isandrocks/Skyline_20K/20Key_macropad.kicad_sch

## KiCad design 20Key_macropad.kicad_sch (2024-02-22)

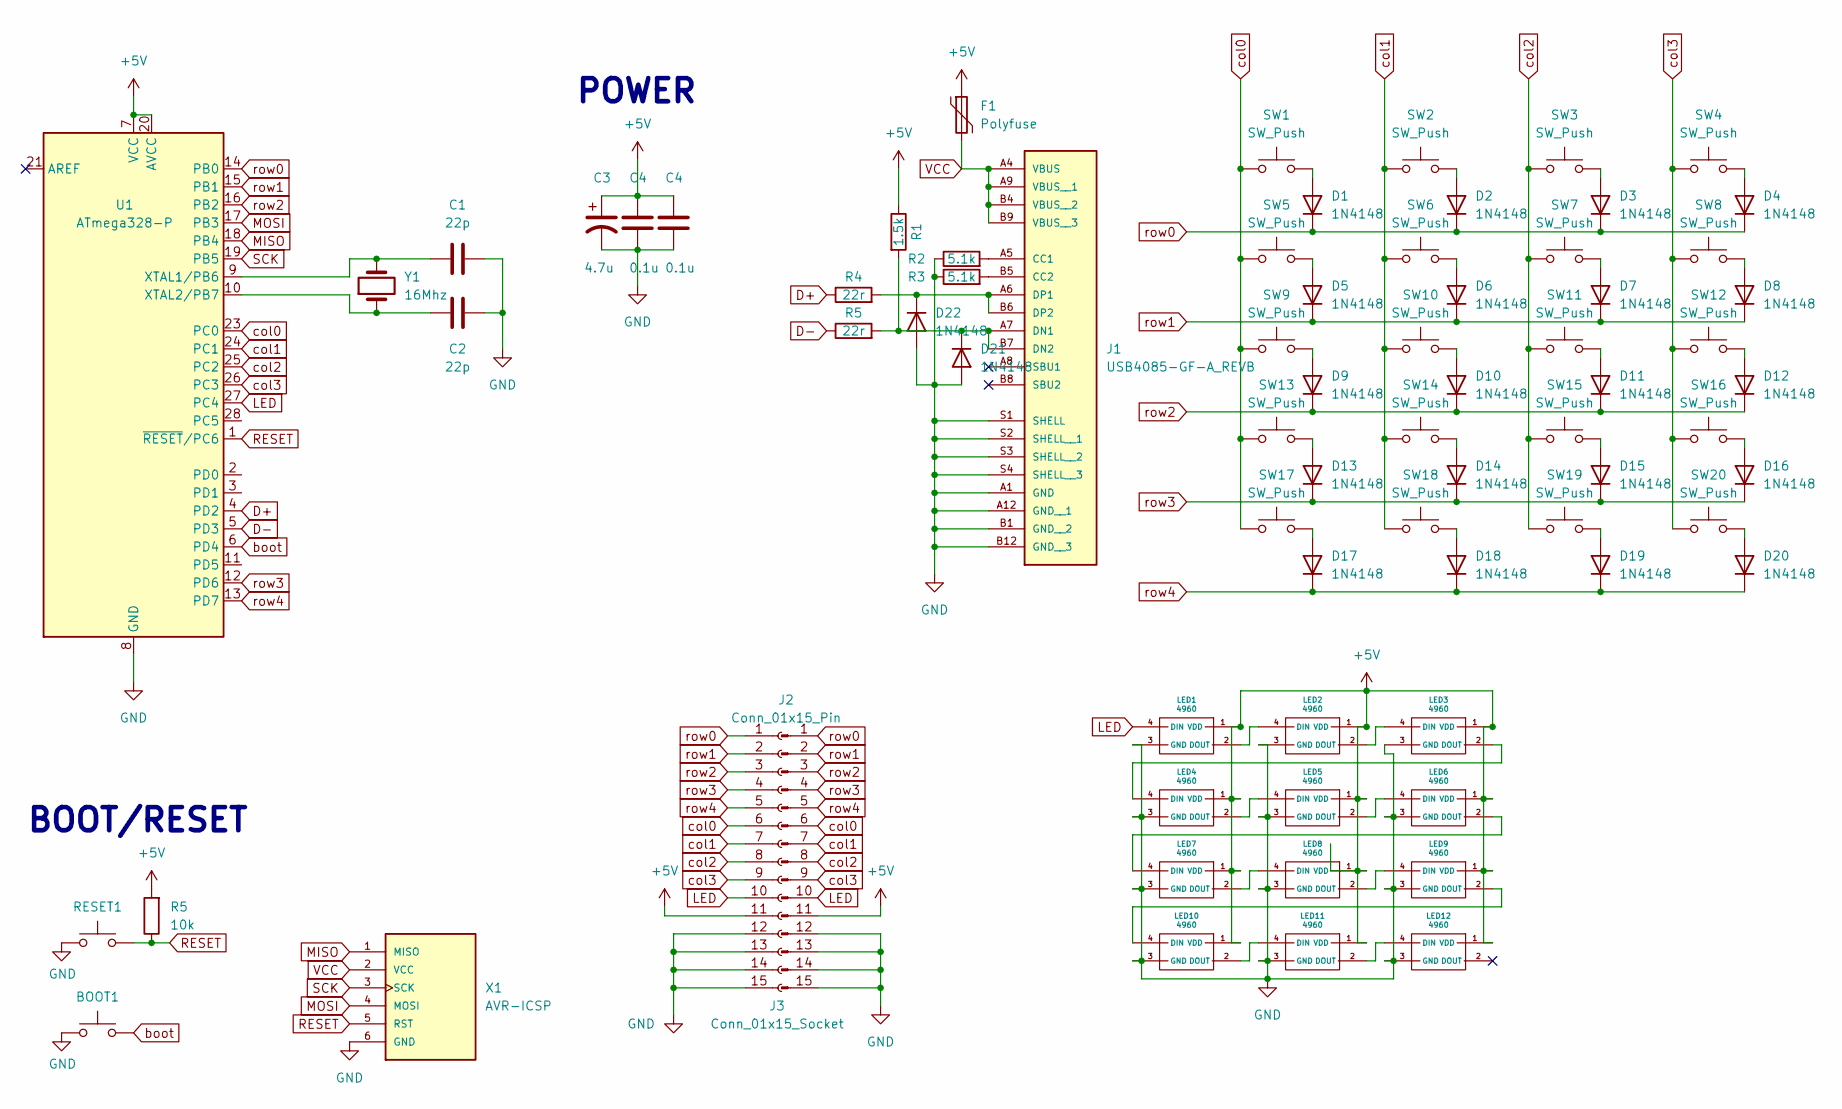
[picture p2: schematic 20Key_macropad.kicad_sch]

Parts:
BOOT1: SW_Push; SW_PUSH_6mm
C1, C2: 22p; C_Disc_D4.3mm_W1.9mm_P5.00mm
C3: 4.7u; CP_Radial_D5.0mm_P2.50mm
C4: 0.1u; C_Disc_D3.0mm_W2.0mm_P2.50mm
D1, D2, D3, D4, D5, D6, D7, D8, D9, D10, D11, D12, D13, D14, D15, D16, D17, D18, D19, D20: 1N4148; D_SOD-123
D21, D22: 1N4148; D_DO-35_SOD27_P7.62mm_Horizontal
F1: Polyfuse; C_Disc_D7.5mm_W2.5mm_P5.00mm
J1: USB4085-GF-A_REVB; GCT_USB4085-GF-A_REVB; PARTREV B
J2: Conn_01x15_Pin; PinHeader_1x15_P2.54mm_Vertical
J3: Conn_01x15_Socket; PinHeader_1x15_P2.54mm_Vertical
LED1, LED2, LED3, LED4, LED5, LED6, LED7, LED8, LED9, LED10, LED11, LED12: 4960; 4960_ADA
R1: 1.5k; R_Axial_DIN0204_L3.6mm_D1.6mm_P5.08mm_Horizontal
R2, R3: 5.1k; R_Axial_DIN0204_L3.6mm_D1.6mm_P5.08mm_Horizontal
R4: 22r; R_Axial_DIN0204_L3.6mm_D1.6mm_P5.08mm_Horizontal
R5: 10k; R_Axial_DIN0204_L3.6mm_D1.6mm_P5.08mm_Horizontal
RESET1: SW_Push; SW_PUSH_6mm
SW1, SW2, SW3, SW4, SW5, SW6, SW7, SW8, SW9, SW10, SW11, SW12, SW13, SW14, SW15, SW16, SW17, SW18, SW19, SW20: SW_Push; SW_Cherry_MX_1.00u_PCB
U1: ATmega328-P; DIP-28_W7.62mm
X1: AVR-ICSP; AVR-ICSP_ICSP-2X03-2.54
Y1: 16Mhz; Crystal_HC49-4H_Vertical

Connections:
+5V: C3.1, C4.1, F1.1, J2.11, J3.11, LED1.1 (VDD), LED2.1 (VDD), LED3.1 (VDD), LED4.1 (VDD), LED5.1 (VDD), LED6.1 (VDD), LED7.1 (VDD), LED8.1 (VDD), LED9.1 (VDD), LED10.1 (VDD), LED11.1 (VDD), LED12.1 (VDD), R1.1, R5.2, U1.7 (VCC), U1.20 (AVCC)
D+: R4.1, U1.4 (PD2)
D-: R5.1, U1.5 (PD3)
GND: BOOT1.1, C1.2, C2.2, C3.2, C4.2, D21.2 (A), D22.2 (A), J1.A1 (GND), J1.A12 (GND__1), J1.B1 (GND__2), J1.B12 (GND__3), J1.S1 (SHELL), J1.S2 (SHELL__1), J1.S3 (SHELL__2), J1.S4 (SHELL__3), J2.12, J2.13, J2.14, J2.15, J3.12, J3.13, J3.14, J3.15, LED1.3 (GND), LED2.3 (GND), LED3.3 (GND), LED4.3 (GND), LED5.3 (GND), LED6.3 (GND), LED7.3 (GND), LED8.3 (GND), LED9.3 (GND), LED10.3 (GND), LED11.3 (GND), LED12.3 (GND), R2.1, R3.1, RESET1.1, U1.8 (GND), U1.22 (GND), X1.6 (GND)
LED: J2.10, J3.10, LED1.4 (DIN), U1.27 (PC4)
MISO: U1.18 (PB4), X1.1 (MISO)
MOSI: U1.17 (PB3), X1.4 (MOSI)
unnamed: C1.1, U1.9 (XTAL1/PB6), Y1.2
unnamed: C2.1, U1.10 (XTAL2/PB7), Y1.1
unnamed: D1.2 (A), SW1.2
unnamed: D2.2 (A), SW2.2
unnamed: D3.2 (A), SW3.2
unnamed: D4.2 (A), SW4.2
unnamed: D5.2 (A), SW5.2
unnamed: D6.2 (A), SW6.2
unnamed: D7.2 (A), SW7.2
unnamed: D8.2 (A), SW8.2
unnamed: D9.2 (A), SW9.2
unnamed: D10.2 (A), SW10.2
unnamed: D11.2 (A), SW11.2
unnamed: D12.2 (A), SW12.2
unnamed: D13.2 (A), SW13.2
unnamed: D14.2 (A), SW14.2
unnamed: D15.2 (A), SW15.2
unnamed: D16.2 (A), SW16.2
unnamed: D17.2 (A), SW17.2
unnamed: D18.2 (A), SW18.2
unnamed: D19.2 (A), SW19.2
unnamed: D20.2 (A), SW20.2
unnamed: D21.1 (K), J1.A7 (DN1), J1.B7 (DN2), R1.2, R5.2
unnamed: D22.1 (K), J1.A6 (DP1), J1.B6 (DP2), R4.2
unnamed: J1.A5 (CC1), R2.2
unnamed: J1.B5 (CC2), R3.2
unnamed: LED1.2 (DOUT), LED2.4 (DIN)
unnamed: LED2.2 (DOUT), LED3.4 (DIN)
unnamed: LED3.2 (DOUT), LED4.4 (DIN)
unnamed: LED4.2 (DOUT), LED5.4 (DIN)
unnamed: LED5.2 (DOUT), LED6.4 (DIN)
unnamed: LED6.2 (DOUT), LED7.4 (DIN)
unnamed: LED7.2 (DOUT), LED8.4 (DIN)
unnamed: LED8.2 (DOUT), LED9.4 (DIN)
unnamed: LED10.2 (DOUT), LED11.4 (DIN)
unnamed: LED9.2 (DOUT), LED10.4 (DIN)
unnamed: LED11.2 (DOUT), LED12.4 (DIN)
RESET: R5.1, RESET1.2, U1.1 (~RESET/PC6), X1.5 (RST)
SCK: U1.19 (PB5), X1.3 (SCK)
VCC: F1.2, J1.A4 (VBUS), J1.A9 (VBUS__1), J1.B4 (VBUS__2), J1.B9 (VBUS__3), X1.2 (VCC)
boot: BOOT1.2, U1.6 (PD4)
col0: J2.6, J3.6, SW1.1, SW5.1, SW9.1, SW13.1, SW17.1, U1.23 (PC0)
col1: J2.7, J3.7, SW2.1, SW6.1, SW10.1, SW14.1, SW18.1, U1.24 (PC1)
col2: J2.8, J3.8, SW3.1, SW7.1, SW11.1, SW15.1, SW19.1, U1.25 (PC2)
col3: J2.9, J3.9, SW4.1, SW8.1, SW12.1, SW16.1, SW20.1, U1.26 (PC3)
row0: D1.1 (K), D2.1 (K), D3.1 (K), D4.1 (K), J2.1, J3.1, U1.14 (PB0)
row1: D5.1 (K), D6.1 (K), D7.1 (K), D8.1 (K), J2.2, J3.2, U1.15 (PB1)
row2: D9.1 (K), D10.1 (K), D11.1 (K), D12.1 (K), J2.3, J3.3, U1.16 (PB2)
row3: D13.1 (K), D14.1 (K), D15.1 (K), D16.1 (K), J2.4, J3.4, U1.12 (PD6)
row4: D17.1 (K), D18.1 (K), D19.1 (K), D20.1 (K), J2.5, J3.5, U1.13 (PD7)

Notes on the sheet:
BOOT/RESET
POWER
